luklab63/PAL-cube/PAL V1/3D models/normal model/normal body.STL

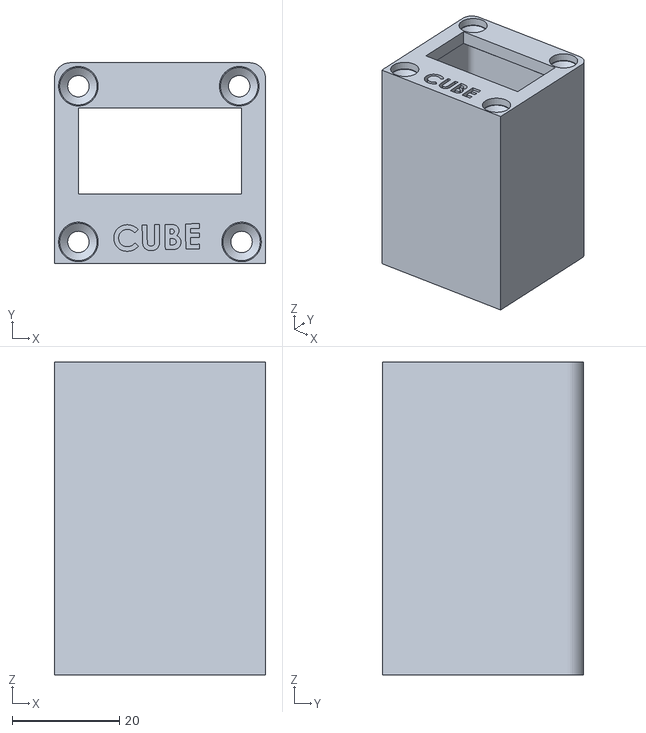
[picture p20: CAD file, 2026-03-22, an earlier design]
PAL V1/3D models/normal model/normal body.STL
39.5 x 37.5 x 58.5
