luklab63/PAL-cube/PAL V1/3D models/solidworks/front pal case.step

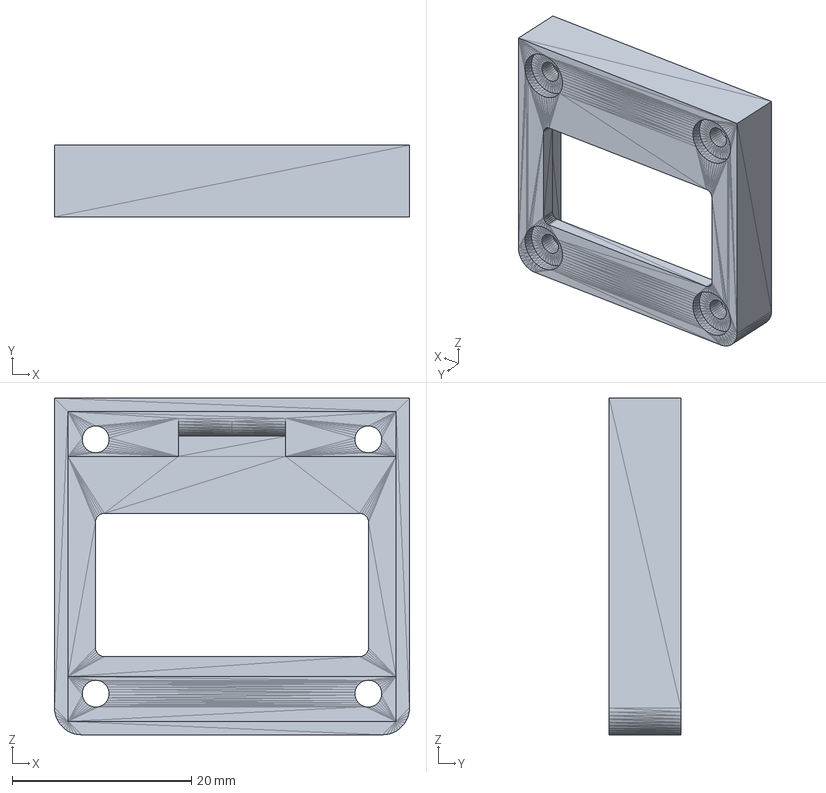
[picture p21: CAD file, 2026-03-22, an earlier design]
PAL V1/3D models/solidworks/front pal case.step
39.7 x 8.00 x 37.6 mm
