luklab63/PAL-cube/PAL V2/PALV2/bitmap.hpp

#ifndef BITMAP_HPP // met le nom de ton fichier en majuscule, c'est pas grave si y'a une erreur, il faut juste que les deux soit les mm
#define BITMAP_HPP
// 'blink', 128x64px


static const unsigned char default_face [] PROGMEM= {
0xff,0xff,0xff,0xff,0xff,0xff,0xff,0xff,0xff,0xff,0xff,0xff,0xff,0xff,0xff,
 0xff,0xff,0xff,0xff,0xff,0xff,0xff,0xff,0xff,0xff,0xff,0xff,0xff,0xff,0xff,
 0xff,0xff,0xff,0xff,0xff,0xff,0xff,0xff,0xff,0xff,0xff,0xff,0xff,0xff,0xff,
 0xff,0xff,0xff,0xff,0xff,0xff,0xff,0xff,0xff,0xff,0xff,0xff,0xff,0xff,0xff,
 0xff,0xff,0xff,0xff,0xff,0xff,0xff,0xff,0x01,0xfc,0xff,0xff,0xff,0xff,0x3f,
 0x80,0xff,0xff,0xff,0xff,0xff,0xff,0xff,0x1f,0xfe,0xc3,0xff,0xff,0xff,0xff,
 0xc3,0x7f,0xf8,0xff,0xff,0xff,0xff,0xff,0xff,0xe3,0xff,0x1f,0xfe,0xff,0xff,
 0x7f,0xf8,0xff,0xc7,0xff,0xff,0xff,0xff,0xff,0xff,0xf9,0xff,0xff,0xf0,0xff,
 0xff,0x0f,0xff,0xff,0x9f,0xff,0xff,0xff,0xff,0xff,0xff,0xff,0x1f,0xff,0x87,
 0xff,0xff,0xe1,0xff,0xf8,0xff,0xff,0xff,0xff,0xff,0xff,0xff,0xff,0x03,0xfc,
 0xbf,0xff,0xff,0xfd,0x3f,0xc0,0xff,0xff,0xff,0xff,0xff,0xff,0xff,0xff,0x01,
 0xf8,0x3f,0xff,0xff,0xfc,0x1f,0x80,0xff,0xff,0xff,0xff,0xff,0xff,0xff,0x7f,
 0x00,0xe0,0x7f,0xfe,0x7f,0xfe,0x07,0x00,0xfe,0xff,0xff,0xff,0xff,0xff,0xff,
 0x3f,0x00,0xc0,0xff,0xff,0xff,0xff,0x03,0x00,0xfc,0xff,0xff,0xff,0xff,0xff,
 0xff,0x3f,0x00,0x80,0xff,0xff,0xff,0xff,0x01,0x00,0xfc,0xff,0xff,0xff,0xff,
 0xff,0xff,0x1f,0x00,0x80,0xff,0xff,0xff,0xff,0x01,0x00,0xf8,0xff,0xff,0xff,
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
	0xff,0xff,0xff,0xff,0xff,0xff,0xff,0xff,0xff,0xff,0xff,0xff,0xff,0xff,0xff,
	0xff,0xff,0xff,0xff,0xff,0xff,0xff,0xff,0xff,0xff,0xff,0xff,0xff,0xff,0xff,
	0xff,0xff,0xff,0xff,0xff,0xff,0xff,0xff,0xff,0xff,0xff,0xff,0xff,0xff,0xff,
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
 };

#endif
